warmech/lisa-cpu-card/cad/cpu-card.kicad_sch

## KiCad design cad/cpu-card.kicad_sch (2024-03-19)

Schematic: cpu-card.kicad_sch

Parts:
C1, C2, C3, C4, C5, C6, C7, C10, C11, C12, C13, C14, C15, C16, C17, C18, C20, C22, C23, C24, C25, C26, C27, C28, C29, C30, C31, C32, C33, C34, C35, C36, C37, C38, C41: 0.1uF 50V; C_Axial_L3.8mm_D2.6mm_P10.00mm_Horizontal
C8: 2.2uF; CP_Axial_L11.0mm_D5.0mm_P18.00mm_Horizontal
C9: 0.01uF; R_Axial_DIN0309_L9.0mm_D2.54mm_P12.70mm_Horizontal
C19, C21: 220pF; C_Rect_L9.0mm_W2.5mm_P7.50mm_MKT
C39: 0.1uF; R_Axial_DIN0309_L9.0mm_D2.54mm_P12.70mm_Horizontal
C40, C42: 220uF / 16V; CP_Axial_L11.0mm_D5.0mm_P18.00mm_Horizontal
C43: 0.1uF 50V; C_Rect_L9.0mm_W2.5mm_P7.50mm_MKT
CR1: 1N4148; D_DO-35_SOD27_P7.62mm_Horizontal
J1: Apple Lisa CPU Card Edge Connector; Apple_Lisa_CPU_CardEdge
J2: Conn_01x03; PinHeader_1x03_P2.54mm_Vertical
J3, J4: PinHeader_1x02_P2.54mm_Vertical
L1: L; R_Axial_DIN0309_L9.0mm_D2.54mm_P12.70mm_Horizontal
OSC1: 20.37504 MHz; Oscillator_DIP-14
Q1, Q2: PN4258; TO-92
R1, R11, R17: 1.5K; R_Axial_DIN0309_L9.0mm_D2.54mm_P12.70mm_Horizontal
R2: 470K; R_Axial_DIN0309_L9.0mm_D2.54mm_P12.70mm_Horizontal
R3: 5.1K; R_Axial_DIN0309_L9.0mm_D2.54mm_P12.70mm_Horizontal
R4, R7, R8, R13: 150; R_Axial_DIN0309_L9.0mm_D2.54mm_P12.70mm_Horizontal
R5, R6, R12: 3.3K; R_Axial_DIN0309_L9.0mm_D2.54mm_P12.70mm_Horizontal
R9, R16: 1K; R_Axial_DIN0309_L9.0mm_D2.54mm_P12.70mm_Horizontal
R10: 22; R_Axial_DIN0309_L9.0mm_D2.54mm_P12.70mm_Horizontal
R14: 330; R_Axial_DIN0309_L9.0mm_D2.54mm_P12.70mm_Horizontal
R15: 47; R_Axial_DIN0309_L9.0mm_D2.54mm_P12.70mm_Horizontal
RP1, RP2: R_Pack15_Split; DIP-16_W7.62mm
U1A1, U2D1: 74LS32; DIP-14_W7.62mm
U1B1: 74LS04; DIP-14_W7.62mm
U1C1: 74LS169; DIP-16_W7.62mm
U1D1, U13F1: 74LS138; DIP-16_W7.62mm
U1E1: 74S132; DIP-14_W7.62mm
U2B1, U3B1, U3C1, U4B1: 74LS109; DIP-16_W7.62mm
U2C1, U3D1: 74LS260; DIP-14_W7.62mm
U2E1: 7417; DIP-14_W7.62mm
U3A1, U3E1, U5D1: 74S109; DIP-16_W7.62mm
U4A1: 74LS08; DIP-14_W7.62mm
U4D1: 74S86; DIP-14_W7.62mm
U4E1: 74LS259; DIP-16_W7.62mm
U4F1: 74LS156; DIP-16_W7.62mm
U5A1: 74F10; DIP-14_W7.62mm
U5B1, U6A1: 74F02; DIP-14_W7.62mm
U5C1: 74LS279; DIP-16_W7.62mm
U5E1, U6F1, U7B1: 74LS393; DIP-14_W7.62mm
U5F1, U6E1, U7E1, U8E1: 74LS153; DIP-16_W7.62mm
U6B1, U7D1, U11C1, U11D1, U11E1, U13E1: 74LS374; DIP-20_W7.62mm
U6C1: 6309; DIP-20_W7.62mm
U6D1, U7C1, U15F1: 74LS00; DIP-14_W7.62mm
U7A1: 74LS38; DIP-14_W7.62mm
U7F1, U8F1: 74LS166; DIP-16_W7.62mm
U8A1, U9A1, U10A1: 2148H; DIP-18_W7.62mm
U8B1, U9B1, U10B1: 74F283; DIP-16_W7.62mm
U8C1, U9E1, U15C1: 74LS244; DIP-20_W7.62mm
U9D1: 74LS373; DIP-20_W7.62mm
U9F1, U11A1, U11B1, U11F1, U14E1, U15E1: 74LS245; DIP-20_W7.62mm
U10C1: 74LS11; DIP-14_W7.62mm
U12F1: 74LS148; DIP-16_W7.62mm
U13A1: 68000; DIP-64_W22.86mm
U14F1: 74LS139; DIP-16_W7.62mm
U15B1: LM556; DIP-14_W7.62mm
UD13, UD14: 2764; DIP-28_W15.24mm
Y1: Crystal; Crystal_HC18-U_Horizontal_1EP_style1

Connections:
+5V: C1.2, C2.2, C3.2, C4.2, C5.2, C6.2, C7.2, C9.1, C10.2, C11.2, C12.2, C13.2, C14.2, C15.2, C16.2, C17.2, C18.2, C20.2, C22.2, C23.2, C24.2, C25.2, C26.2, C27.2, C28.2, C29.2, C30.2, C31.2, C32.2, C33.2, C34.2, C35.2, C36.2, C37.2, C38.2, C40.1, C41.2, C42.1, CR1.1 (K), J1.19 (+5V), J1.20 (+5V), J1.45 (+5V), J1.46 (+5V), J1.91 (+5V), J1.92 (+5V), J1.119 (+5V), J1.120 (+5V), J2.3, OSC1.14 (Vcc), R1.1, R2.1, R3.1, R5.1, R6.1, R11.1, R12.1, RP1.16, RP2.16, U1A1.14 (VCC), U1B1.14 (VCC), U1C1.16 (VCC), U1D1.16 (VCC), U1E1.14 (VCC), U2B1.16 (VCC), U2C1.14 (VCC), U2D1.14 (VCC), U2E1.14 (VCC), U3A1.16 (VCC), U3B1.16 (VCC), U3C1.16 (VCC), U3D1.14 (VCC), U3E1.16 (VCC), U4A1.14 (VCC), U4B1.16 (VCC), U4D1.14 (VCC), U4E1.16 (VCC), U4F1.16 (VCC), U5A1.14 (VCC), U5B1.14 (VCC), U5C1.16 (VCC), U5D1.16 (VCC), U5E1.14 (VCC), U5F1.16 (VCC), U6A1.14 (VCC), U6B1.20 (VCC), U6C1.20 (VCC), U6D1.14 (VCC), U6E1.16 (VCC), U6F1.14 (VCC), U7A1.14 (VCC), U7B1.14 (VCC), U7C1.14 (VCC), U7D1.20 (VCC), U7E1.16 (VCC), U7F1.16 (VCC), U8A1.18 (VCC), U8B1.16 (VCC), U8C1.20 (VCC), U8E1.16 (VCC), U8F1.16 (VCC), U9A1.18 (VCC), U9B1.16 (VCC), U9D1.20 (VCC), U9E1.20 (VCC), U9F1.20 (VCC), U10A1.18 (VCC), U10B1.16 (VCC), U10C1.14 (VCC), U11A1.20 (VCC), U11B1.20 (VCC), U11C1.20 (VCC), U11D1.20 (VCC), U11E1.20 (VCC), U11F1.20 (VCC), U12F1.16 (VCC), U13A1.14 (VCC), U13A1.49 (VCC), U13E1.20 (VCC), U13F1.16 (VCC), U14E1.20 (VCC), U14F1.16 (VCC), U15B1.4 (RST), U15B1.10 (RST), U15B1.14 (VCC), U15C1.20 (VCC), U15E1.20 (VCC), U15F1.14 (VCC), UD13.1 (VPP), UD13.26 (NC), UD13.27 (~PGM), UD13.28 (VCC), UD14.26 (NC), UD14.27 (~PGM), UD14.28 (VCC)
+12V: J1.61 (+12V), R14.2, R17.2
A1: J1.47 (A1), U4E1.13 (D), U4F1.13 (A0), U7E1.6 (I0a), U15C1.3 (O3b)
A2: J1.48 (A2), U4E1.1 (A0), U4F1.3 (A1), U7E1.10 (I0b), U15C1.5 (O2b)
A3: J1.49 (A3), U4E1.2 (A1), U4F1.1 (Ea1), U4F1.15 (Eb2), U6E1.6 (I0a), U15C1.7 (O1b)
A4: J1.50 (A4), U4E1.3 (A2), U6E1.10 (I0b), U15C1.9 (O0b)
A5: J1.51 (A5), U5F1.6 (I0a), U15C1.12 (O3a)
A6: J1.52 (A6), U5F1.10 (I0b), U11E1.4 (D1), U15C1.14 (O2a)
A7: J1.53 (A7), U8E1.6 (I0a), U11E1.7 (D2), U15C1.16 (O1a)
A8: J1.54 (A8), U8E1.10 (I0b), U11E1.8 (D3), U15C1.18 (O0a)
A9: J1.55 (A9), U7E1.4 (I2a), U11D1.12 (O4), U11E1.13 (D4)
A10: J1.56 (A10), U7E1.12 (I2b), U11D1.15 (O5), U11E1.14 (D5)
A11: J1.57 (A11), U6E1.4 (I2a), U11D1.16 (O6), U11E1.17 (D6), U14F1.14 (A0)
A12: J1.58 (A12), U6E1.12 (I2b), U11D1.19 (O7), U11E1.18 (D7), U14F1.13 (A1)
A13: U5F1.4 (I2a), U7D1.2 (O0), U9D1.2 (O0), U13E1.3 (D0)
A14: U5F1.12 (I2b), U7D1.5 (O1), U9D1.5 (O1), U13E1.4 (D1)
A15: U7D1.6 (O2), U8E1.3 (I3a), U8E1.4 (I2a), U9D1.6 (O2), U11C1.6 (O2), U13E1.7 (D2)
A16: J1.102 (A16), U7D1.9 (O3), U8E1.12 (I2b), U8E1.13 (I3b), U9D1.9 (O3), U11C1.9 (O3), U13E1.8 (D3)
A17: J1.103 (A17), U7D1.12 (O4), U9D1.12 (O4), U11C1.12 (O4), U13E1.13 (D4)
A18: J1.104 (A18), U7D1.15 (O5), U9D1.15 (O5), U11C1.15 (O5), U13E1.14 (D5)
A19: J1.105 (A19), U7D1.16 (O6), U9D1.16 (O6), U11C1.16 (O6), U13E1.17 (D6)
A20: J1.110 (A20), U7D1.19 (O7), U9D1.19 (O7), U11C1.19 (O7), U13E1.18 (D7)
ACCK: U3D1.3, U4D1.1, U9B1.9 (C4), U10B1.7 (C0)
AS: U2B1.15 (~R), U2E1.13, U3A1.5 (~S), U3B1.1 (~R), U3B1.15 (~R), U4B1.1 (~R), U6A1.1
BD0: J1.27 (BD0), U9E1.18 (O0a), U9F1.18 (B0), U11E1.2 (O0), U15E1.2 (A0)
BD1: J1.28 (BD1), U9E1.16 (O1a), U9F1.17 (B1), U11E1.5 (O1), U15E1.3 (A1)
BD2: J1.29 (BD2), U9E1.14 (O2a), U9F1.16 (B2), U11E1.6 (O2), U15E1.4 (A2)
BD3: J1.30 (BD3), U9E1.12 (O3a), U9F1.15 (B3), U11E1.9 (O3), U15E1.5 (A3)
BD4: J1.31 (BD4), U9E1.9 (O0b), U9F1.14 (B4), U11E1.12 (O4), U15E1.6 (A4)
BD5: J1.32 (BD5), U7D1.3 (D0), U9E1.7 (O1b), U9F1.13 (B5), U11E1.15 (O5), U15E1.7 (A5)
BD6: J1.33 (BD6), U7D1.4 (D1), U9E1.5 (O2b), U9F1.12 (B6), U11E1.16 (O6), U15E1.8 (A6)
BD7: J1.34 (BD7), U7D1.7 (D2), U9E1.3 (O3b), U9F1.11 (B7), U11E1.19 (O7), U15E1.9 (A7)
BD8: J1.35 (BD8), U7D1.8 (D3), U11F1.18 (B0), U13E1.2 (O0), U14E1.2 (A0)
BD9: J1.36 (BD9), U7D1.13 (D4), U11F1.17 (B1), U13E1.5 (O1), U14E1.3 (A1)
BD10: J1.37 (BD10), U7D1.14 (D5), U11F1.16 (B2), U13E1.6 (O2), U14E1.4 (A2)
BD11: J1.38 (BD11), U7D1.17 (D6), U11F1.15 (B3), U13E1.9 (O3), U14E1.5 (A3)
BD12: J1.39 (BD12), U7D1.18 (D7), U11F1.14 (B4), U13E1.12 (O4), U14E1.6 (A4)
BD13: J1.40 (BD13), U11F1.13 (B5), U13E1.15 (O5), U14E1.7 (A5)
BD14: J1.41 (BD14), U11F1.12 (B6), U13E1.16 (O6), U14E1.8 (A6)
BD15: J1.42 (BD15), U11F1.11 (B7), U13E1.19 (O7), U14E1.9 (A7)
BGACK: U3D1.1, U3D1.8, U6A1.13, U6D1.4, U7C1.12, U8C1.19 (OEb), U11D1.1 (OE), U15C1.1 (OEa), U15C1.19 (OEb)
CAS: U2C1.1, U3A1.4 (C), U3C1.9 (~Q), U10C1.3
CK: U1C1.2 (CP), U1E1.6, U2B1.4 (C), U2B1.12 (C), U3A1.12 (C), U3B1.4 (C), U3B1.12 (C), U3C1.4 (C), U3C1.12 (C), U4B1.4 (C), U4B1.12 (C)
CMUX: U2D1.10, U4A1.4, U4B1.10 (Q), U6D1.5, U11C1.1 (OE), U15F1.10
CPUC1: U1A1.1, U2B1.6 (Q), U5A1.9, U7C1.13
CPUCK: J1.22 (CPUCK), R10.1
DOTCK: J1.106 (DOTCK), U1E1.8, U3E1.4 (C), U3E1.12 (C), U5D1.4 (C), U5D1.12 (C), U7F1.7 (Clk), U8F1.7 (Clk)
E: J1.16 (E), U8C1.14 (O2a)
FC2: U7C1.2, U10C1.11, U13A1.26 (FC2)
GND: C1.1, C2.1, C3.1, C4.1, C5.1, C6.1, C7.1, C8.2, C10.1, C11.1, C12.1, C13.1, C14.1, C15.1, C16.1, C17.1, C18.1, C19.2, C20.1, C21.2, C22.1, C23.1, C24.1, C25.1, C26.1, C27.1, C28.1, C29.1, C30.1, C31.1, C32.1, C33.1, C34.1, C35.1, C36.1, C37.1, C38.1, C39.2, C40.2, C41.1, C42.2, C43.2, J1.17 (GND), J1.18 (GND), J1.43 (GND), J1.44 (GND), J1.89 (GND), J1.90 (GND), J1.117 (GND), J1.118 (GND), J3.1, J4.1, L1.2, OSC1.7 (GND), R9.1, R13.2, R16.2, U1A1.7 (GND), U1B1.7 (GND), U1C1.3 (P0), U1C1.4 (P1), U1C1.5 (P2), U1C1.6 (P3), U1C1.7 (~CEP), U1C1.8 (GND), U1C1.10 (~CET), U1D1.4 (E1), U1D1.5 (E2), U1D1.8 (GND), U1E1.7 (GND), U2B1.8 (GND), U2C1.7 (GND), U2D1.7 (GND), U2E1.7 (GND), U3A1.2 (J), U3A1.8 (GND), U3B1.8 (GND), U3C1.8 (GND), U3D1.7 (GND), U3E1.8 (GND), U4A1.7 (GND), U4A1.9, U4A1.10, U4B1.8 (GND), U4D1.7 (GND), U4D1.12, U4E1.8 (GND), U4F1.8 (GND), U5A1.7 (GND), U5B1.7 (GND), U5C1.8 (GND), U5D1.2 (J), U5D1.8 (GND), U5E1.7 (GND), U5F1.1 (Ea), U5F1.8 (GND), U5F1.15 (Eb), U6A1.7 (GND), U6B1.1 (OE), U6B1.10 (GND), U6C1.10 (GND), U6C1.15 (/E1(P)), U6C1.16 (/E2), U6D1.7 (GND), U6E1.1 (Ea), U6E1.8 (GND), U6E1.15 (Eb), U6F1.7 (GND), U7A1.7 (GND), U7B1.7 (GND), U7C1.7 (GND), U7D1.10 (GND), U7E1.1 (Ea), U7E1.8 (GND), U7E1.15 (Eb), U7F1.8 (GND), U8A1.8 (/CS), U8A1.9 (GND), U8B1.8 (GND), U8C1.1 (OEa), U8C1.10 (GND), U8E1.1 (Ea), U8E1.8 (GND), U8E1.15 (Eb), U8F1.8 (GND), U9A1.8 (/CS), U9A1.9 (GND), U9B1.8 (GND), U9D1.10 (GND), U9E1.10 (GND), U9F1.10 (GND), U10A1.9 (GND), U10B1.2 (B2), U10B1.6 (B1), U10B1.8 (GND), U10B1.11 (B4), U10B1.15 (B3), U10C1.7 (GND), U11A1.10 (GND), U11B1.10 (GND), U11C1.3 (D0), U11C1.4 (D1), U11C1.10 (GND), U11D1.10 (GND), U11E1.10 (GND), U11F1.10 (GND), U12F1.5 (EI), U12F1.8 (GND), U13A1.16 (GND), U13A1.53 (GND), U13E1.10 (GND), U13F1.8 (GND), U14E1.10 (GND), U14F1.8 (GND), U15B1.7 (GND), U15C1.10 (GND), U15E1.10 (GND), U15F1.7 (GND), UD13.14 (GND), UD13.20 (~CE), UD14.14 (GND), UD14.20 (~CE)
IAK: U1B1.5, U2C1.9, U10C1.8
INVID: J3.2, RP1.10, U4D1.10, U8F1.1 (Ds), U9E1.15 (I2b)
IOA13: U11D1.2 (O0), U13F1.1 (A0)
IOA14: U11D1.5 (O1), U13F1.2 (A1)
IOA15: U11D1.6 (O2), U13F1.3 (A2)
IOA16: RP2.5, U11D1.9 (O3), U13F1.5 (E2)
IOCY: U2C1.2, U2C1.8, U3A1.13 (~K), U3A1.14 (J), U3A1.15 (~R), U4B1.6 (Q)
MALE: U2B1.9 (~Q), U9D1.11 (LE)
MD0: J1.73 (MD0), U8F1.2 (A), U9F1.2 (A0)
MD1: J1.74 (MD1), U8F1.3 (B), U9F1.3 (A1)
MD2: J1.75 (MD2), U8F1.4 (C), U9F1.4 (A2)
MD3: J1.76 (MD3), U8F1.5 (D), U9F1.5 (A3)
MD4: J1.77 (MD4), U8F1.10 (E), U9F1.6 (A4)
MD5: J1.78 (MD5), U8F1.11 (F), U9F1.7 (A5)
MD6: J1.79 (MD6), U8F1.12 (G), U9F1.8 (A6)
MD7: J1.80 (MD7), U8F1.14 (H), U9F1.9 (A7)
MD8: J1.81 (MD8), U7F1.2 (A), U11F1.2 (A0)
MD9: J1.82 (MD9), U7F1.3 (B), U11F1.3 (A1)
MD10: J1.83 (MD10), U7F1.4 (C), U11F1.4 (A2)
MD11: J1.84 (MD11), U7F1.5 (D), U11F1.5 (A3)
MD12: J1.85 (MD12), U7F1.10 (E), U11F1.6 (A4)
MD13: J1.86 (MD13), U7F1.11 (F), U11F1.7 (A5)
MD14: J1.87 (MD14), U7F1.12 (G), U11F1.8 (A6)
MD15: J1.88 (MD15), U7F1.14 (H), U11F1.9 (A7)
MMUIO: U1A1.4, U1B1.12, U5D1.5 (~S), U5D1.11 (~S), U6D1.12
MREAD: J1.107 (MREAD), U1E1.11
unnamed: C9.2, R3.2, U2E1.12, U15B1.8 (TRG), U15B1.12 (THR)
unnamed: C19.1, R4.2, R5.2, U5C1.1 (/1R)
unnamed: C21.1, R6.2, R7.2, U5C1.10 (/3R)
unnamed: C39.1, Q1.2 (B), R15.2, R16.1, R17.1
unnamed: L1.1, Q1.3 (C), Y1.1
unnamed: OSC1.8 (OUT), Q2.3 (C), R13.1, U1E1.2
unnamed: Q1.1 (E), Q2.1 (E), R14.1
unnamed: Q2.2 (B), R15.1, Y1.2
unnamed: R8.1, U11A1.9 (A7)
unnamed: R9.2, U10C1.10, U13A1.28 (FC0)
unnamed: R10.2, U4D1.11
unnamed: RP1.2, U1C1.9 (~PE)
unnamed: RP1.3, U9E1.17 (I3b)
unnamed: RP1.6, U1E1.1
unnamed: RP1.8, U1E1.5, U1E1.9
unnamed: RP1.11, U1C1.1 (U/~D), U1D1.6 (E3)
unnamed: RP2.4, U3E1.1 (~R), U3E1.11 (~S), U3E1.15 (~R), U7F1.9 (Clr), U8F1.9 (Clr)
unnamed: RP2.11, U2E1.2, U2E1.3, U13A1.18 (RESET)
unnamed: U1A1.3, U3C1.5 (~S)
unnamed: U1A1.6, U5B1.11
unnamed: U1A1.9, U1A1.10, U1A1.11
unnamed: U1A1.8, U1A1.12, U1A1.13
unnamed: U1B1.2, U3C1.2 (J)
unnamed: U1B1.4, U3C1.14 (J)
unnamed: U1B1.6, U2D1.12
unnamed: U1B1.10, U3D1.11
unnamed: U1C1.12 (Q2), U1D1.3 (A2)
unnamed: U1C1.14 (Q0), U1D1.1 (A0)
unnamed: U1E1.3, U1E1.4, U1E1.10
unnamed: U1E1.12, U1E1.13, U5B1.4, U7A1.9, U7A1.12
unnamed: U2B1.2 (J), U2B1.14 (J), U2C1.6
unnamed: U2C1.5, U3B1.14 (J)
unnamed: U2C1.11, U3B1.10 (Q)
unnamed: U2D1.3, U5A1.2
unnamed: U2D1.6, U5D1.13 (~K)
unnamed: U2D1.11, U4F1.2 (Ea2), U4F1.14 (Eb1)
unnamed: U2E1.5, U3A1.6 (Q)
unnamed: U3A1.7 (~Q), U6A1.8
unnamed: U3B1.2 (J), U3D1.6
unnamed: U3C1.11 (~S), U5A1.6
unnamed: U3D1.4, U5A1.1, U5B1.1
unnamed: U3D1.5, U4B1.2 (J)
unnamed: U3E1.5 (~S), U4A1.11
unnamed: U3E1.6 (Q), U6F1.1 (CP), U7F1.15 (PE), U8F1.15 (PE)
unnamed: U3E1.10 (Q), U4D1.9
unnamed: U3E1.13 (~K), U3E1.14 (J), U7F1.13 (Qh)
unnamed: U4A1.2, U6C1.9 (O4)
unnamed: U4A1.3, U6B1.8 (D3)
unnamed: U4A1.5, U6B1.9 (O3)
unnamed: U4A1.6, U5E1.2 (MR), U5E1.12 (MR), U6F1.2 (MR), U6F1.12 (MR)
unnamed: U4A1.13, U6B1.6 (O2)
unnamed: U4B1.14 (J), U6A1.4
unnamed: U4D1.3, U5A1.13
unnamed: U4E1.4 (Q0), U7A1.10
unnamed: U4E1.5 (Q1), U7A1.13
unnamed: U5A1.4, U7C1.11
unnamed: U5A1.5, U5A1.12
unnamed: U5B1.10, U8B1.7 (C0)
unnamed: U5C1.13 (4Q), U9E1.8 (I3a)
unnamed: U5E1.9 (Q2), U6C1.19 (A7), U6D1.2, U7F1.6 (CE), U8F1.6 (CE)
unnamed: U6B1.2 (O0), U7B1.2 (MR), U7B1.12 (MR)
unnamed: U6B1.3 (D0), U6C1.6 (O1)
unnamed: U6B1.4 (D1), U6C1.7 (O2)
unnamed: U6B1.7 (D2), U6C1.8 (O3)
unnamed: U6B1.13 (D4), U6C1.11 (O5)
unnamed: U6B1.14 (D5), U6C1.12 (O6)
unnamed: U6B1.15 (O5), U6D1.1
unnamed: U6B1.17 (D6), U6B1.18 (D7), U6C1.13 (O7)
unnamed: U6C1.1 (A0), U7B1.3 (Q0)
unnamed: U6C1.2 (A1), U7B1.4 (Q1)
unnamed: U6C1.3 (A2), U7B1.5 (Q2)
unnamed: U6C1.4 (A3), U7B1.6 (Q3), U7B1.13 (CP)
unnamed: U6C1.5 (A4), U7B1.11 (Q0)
unnamed: U6C1.17 (A5), U7B1.10 (Q1)
unnamed: U6D1.6, U7D1.1 (OE)
unnamed: U6D1.10, U6D1.11
unnamed: U7C1.3, U7C1.4, U7C1.10
unnamed: U7F1.1 (Ds), U8F1.13 (Qh)
unnamed: U8B1.9 (C4), U9B1.7 (C0)
unnamed: U7C1.8, U8A1.4 (A3), U9A1.4 (A3), U10A1.4 (A3)
unnamed: U7C1.6, U8A1.5 (A0), U9A1.5 (A0), U10A1.5 (A0)
unnamed: U5B1.8, U6D1.8, U8A1.6 (A1), U9A1.6 (A1), U10A1.6 (A1)
unnamed: U5B1.13, U10A1.8 (/CS)
unnamed: U5D1.10 (Q), U8A1.10 (/WE), U9A1.10 (/WE), U10A1.10 (/WE)
unnamed: U9D1.14 (D5), U10B1.1 (S2)
unnamed: U9D1.13 (D4), U10B1.4 (S1)
unnamed: U9D1.18 (D7), U10B1.10 (S4)
unnamed: U9D1.17 (D6), U10B1.13 (S3)
unnamed: U5C1.9 (3Q), U9E1.4 (I1a), U10C1.1, U10C1.4
unnamed: U5C1.4 (1Q), U9E1.2 (I0a), U10C1.2, U10C1.5
unnamed: U10C1.6, U11E1.11 (Cp), U13E1.11 (Cp)
unnamed: U10C1.9, U13A1.27 (FC1)
unnamed: U5D1.6 (Q), U11A1.19 (CE), U11B1.19 (CE)
unnamed: U11C1.11 (Cp), U15F1.11
unnamed: U9B1.4 (S1), U9D1.3 (D0), U11D1.3 (D0)
unnamed: U9B1.1 (S2), U9D1.4 (D1), U11D1.4 (D1)
unnamed: U9B1.13 (S3), U9D1.7 (D2), U11D1.7 (D2)
unnamed: U9B1.10 (S4), U9D1.8 (D3), U11D1.8 (D3)
unnamed: U8B1.4 (S1), U11D1.13 (D4)
unnamed: U8B1.1 (S2), U11D1.14 (D5)
unnamed: U8B1.13 (S3), U11D1.17 (D6)
unnamed: U8B1.10 (S4), U11D1.18 (D7)
unnamed: U12F1.6 (S2), U13A1.23 (IPL2)
unnamed: U12F1.7 (S1), U13A1.24 (IPL1)
unnamed: U12F1.9 (S0), U13A1.25 (IPL0)
unnamed: U8C1.17 (I3b), U13A1.7 (UDS)
unnamed: U8C1.15 (I2b), U13A1.8 (LDS)
unnamed: U8C1.11 (I0b), U13A1.9 (R/W)
unnamed: U8C1.8 (I3a), U13A1.19 (VMA)
unnamed: U8C1.6 (I2a), U13A1.20 (E)
unnamed: U3A1.10 (Q), U13F1.6 (E3)
unnamed: U2E1.9, U13F1.7 (O7), U14F1.15 (E)
unnamed: U4E1.14 (E), U14F1.12 (O0)
unnamed: U2D1.9, U4D1.6, U15F1.2
unnamed: U9D1.1 (OE), U15F1.8
PCK: U1C1.13 (Q1), U1D1.2 (A1), U4D1.13, U5D1.14 (J), U13A1.15 (CLK)
POR: U7A1.1, U7A1.2, U15B1.5 (Q)
R1: J1.71 (R1), U15F1.3
R2: J1.72 (R2), U2D1.8
RA1: J1.93 (RA1), U7E1.7 (Za)
RA2: J1.94 (RA2), U7E1.9 (Zb)
RA3: J1.95 (RA3), U6E1.7 (Za)
RA4: J1.96 (RA4), U6E1.9 (Zb)
RA5: J1.97 (RA5), U5F1.7 (Za)
RA6: J1.98 (RA6), U5F1.9 (Zb)
RA7: J1.99 (RA7), U8E1.7 (Za)
RA8: J1.100 (RA8), U8E1.9 (Zb)
RAS: U3C1.7 (~Q), U5F1.2 (S1), U6E1.2 (S1), U7E1.2 (S1), U8E1.2 (S1)
READ: J1.64 (READ), RP2.15, U2D1.1, U2D1.5, U5B1.6, U8C1.9 (O0b), U9F1.1 (A->B), U11A1.1 (A->B), U11B1.1 (A->B), U11F1.1 (A->B), U14E1.1 (A->B), U15E1.1 (A->B)
RP1_5: RP1.5, U2B1.1 (~R), U2B1.5 (~S), U2B1.11 (~S), U2B1.13 (~K), U3A1.11 (~S), U3B1.3 (~K), U3B1.5 (~S), U3B1.13 (~K), U3C1.1 (~R), U3C1.15 (~R), U4B1.3 (~K), U4B1.5 (~S), U4B1.11 (~S), U4B1.15 (~R), U5D1.1 (~R), U5D1.15 (~R)
SEG1: U4E1.6 (Q2), U7C1.5
SEG2: U4E1.7 (Q3), U7C1.9
SN: R8.2, U6C1.14 (O8)
SPIO: U2C1.13, U3B1.6 (Q), U6A1.9
TD0: U8A1.14 (I/O1), U8B1.5 (A1), U11B1.2 (A0)
TD1: U8A1.13 (I/O2), U8B1.3 (A2), U11B1.3 (A1)
TD2: U8A1.12 (I/O3), U8B1.14 (A3), U11B1.4 (A2)
TD3: U8A1.11 (I/O4), U8B1.12 (A4), U11B1.5 (A3)
TD4: U9A1.14 (I/O1), U9B1.5 (A1), U11B1.6 (A4)
TD5: U9A1.13 (I/O2), U9B1.3 (A2), U11B1.7 (A5)
TD6: U9A1.12 (I/O3), U9B1.14 (A3), U11B1.8 (A6)
TD7: U9A1.11 (I/O4), U9B1.12 (A4), U11B1.9 (A7)
UA1: U13A1.29 (A1), U15C1.17 (I3b), UD13.10 (A0), UD14.10 (A0)
UA2: U13A1.30 (A2), U15C1.15 (I2b), UD13.9 (A1), UD14.9 (A1)
UA3: U6D1.13, U13A1.31 (A3), U15C1.13 (I1b), UD13.8 (A2), UD14.8 (A2)
UA4: U13A1.32 (A4), U15C1.11 (I0b), UD13.7 (A3), UD14.7 (A3)
UA5: U13A1.33 (A5), U15C1.8 (I3a), UD13.6 (A4), UD14.6 (A4)
UA6: U13A1.34 (A6), U15C1.6 (I2a), UD13.5 (A5), UD14.5 (A5)
UA7: U13A1.35 (A7), U15C1.4 (I1a), UD13.4 (A6), UD14.4 (A6)
UA8: U13A1.36 (A8), U15C1.2 (I0a), UD13.3 (A7), UD14.3 (A7)
UA9: U8B1.6 (B1), U13A1.37 (A9), UD13.25 (A8), UD14.25 (A8)
UA10: U8B1.2 (B2), U13A1.38 (A10), UD13.24 (A9), UD14.24 (A9)
UA11: U8B1.15 (B3), U13A1.39 (A11), UD13.21 (A10), UD14.21 (A10)
UA12: J2.1, J2.2, U8B1.11 (B4), U13A1.40 (A12), UD13.23 (A11), UD14.23 (A11)
UA13: U9B1.6 (B1), U13A1.41 (A13), UD13.2 (A12), UD14.2 (A12)
UA14: U5B1.12, U9B1.2 (B2), U13A1.42 (A14)
UA15: U9B1.15 (B3), U13A1.43 (A15), U14F1.2 (A0)
UA16: U9B1.11 (B4), U13A1.44 (A16), U14F1.3 (A1)
UA17: U8A1.17 (A7), U9A1.17 (A7), U10A1.17 (A7), U13A1.45 (A17)
UA18: U8A1.16 (A8), U9A1.16 (A8), U10A1.16 (A8), U13A1.46 (A18)
UA19: U8A1.15 (A9), U9A1.15 (A9), U10A1.15 (A9), U13A1.47 (A19)
UA20: U8A1.7 (A2), U9A1.7 (A2), U10A1.7 (A2), U13A1.48 (A20)
UA21: U8A1.1 (A6), U9A1.1 (A6), U10A1.1 (A6), U13A1.50 (A21)
UA22: U8A1.2 (A5), U9A1.2 (A5), U10A1.2 (A5), U13A1.51 (A22)
UA23: U8A1.3 (A4), U9A1.3 (A4), U10A1.3 (A4), U13A1.52 (A23)
UD0: U11B1.18 (B0), U11C1.7 (D2), U13A1.5 (D0), U15E1.18 (B0), UD14.11 (D0)
UD1: U11B1.17 (B1), U11C1.8 (D3), U13A1.4 (D1), U15E1.17 (B1), UD14.12 (D1)
UD2: U11B1.16 (B2), U11C1.13 (D4), U13A1.3 (D2), U15E1.16 (B2), UD14.13 (D2)
UD3: U11B1.15 (B3), U11C1.14 (D5), U13A1.2 (D3), U15E1.15 (B3), UD14.15 (D3)
UD4: U11B1.14 (B4), U11C1.17 (D6), U13A1.1 (D4), U15E1.14 (B4), UD14.16 (D4)
UD5: U11B1.13 (B5), U11C1.18 (D7), U13A1.64 (D5), U15E1.13 (B5), UD14.17 (D5)
UD6: U11B1.12 (B6), U13A1.63 (D6), U15E1.12 (B6), UD14.18 (D6)
UD7: U11B1.11 (B7), U13A1.62 (D7), U15E1.11 (B7), UD14.19 (D7)
UD8: U11A1.18 (B0), U13A1.61 (D8), U14E1.18 (B0), UD13.11 (D0)
UD9: U11A1.17 (B1), U13A1.60 (D9), U14E1.17 (B1), UD13.12 (D1)
UD10: U11A1.16 (B2), U13A1.59 (D10), U14E1.16 (B2), UD13.13 (D2)
UD11: U11A1.15 (B3), U13A1.58 (D11), U14E1.15 (B3), UD13.15 (D3)
UD12: U13A1.57 (D12), U14E1.14 (B4), UD13.16 (D4)
UD13: U13A1.56 (D13), U14E1.13 (B5), UD13.17 (D5)
UD14: U11A1.12 (B6), U13A1.55 (D14), U14E1.12 (B6), UD13.18 (D6)
UD15: U11A1.11 (B7), U13A1.54 (D15), U14E1.11 (B7), UD13.19 (D7)
VA1: U6F1.3 (Q0), U7E1.5 (I1a)
VA2: U6F1.4 (Q1), U7E1.11 (I1b)
VA3: U6E1.5 (I1a), U6F1.5 (Q2)
VA4: U6E1.11 (I1b), U6F1.6 (Q3), U6F1.13 (CP)
VA5: U5F1.5 (I1a), U6F1.11 (Q0)
VA6: U5F1.11 (I1b), U6F1.10 (Q1)
VA7: U6F1.9 (Q2), U8E1.5 (I1a)
VA8: U4A1.1, U4D1.4, U5E1.1 (CP), U6F1.8 (Q3), U8E1.11 (I1b)
VA9: U5E1.3 (Q0), U6C1.18 (A6), U7E1.3 (I3a), U8C1.2 (I0a)
VA9B: J1.70 (VA9B), U8C1.18 (O0a)
VA10: U5E1.4 (Q1), U7E1.13 (I3b), U8C1.4 (I1a)
VA10B: J1.69 (VA10B), U8C1.16 (O1a)
VA11: U4D1.5, U5E1.5 (Q2), U6E1.3 (I3a)
VA12: U5E1.6 (Q3), U5E1.13 (CP), U6E1.13 (I3b)
VA13: U5E1.11 (Q0), U5F1.3 (I3a)
VA14: U5E1.10 (Q1), U5F1.13 (I3b)
VID: J1.115 (VID), U4D1.8, U9E1.11 (I0b)
VIDEO: U1A1.2, U1B1.9, U1C1.11 (Q3), U3A1.3 (~K), U4A1.12, U6B1.11 (Cp), U7B1.1 (CP), U11E1.3 (D0)
/AS: J1.63 (/AS), RP1.7, U2C1.4, U6A1.2, U6A1.3, U8C1.7 (O1b)
/BERR: U3B1.9 (~Q), U13A1.22 (BERR)
/BG: J1.26 (/BG), U13A1.11 (BG)
/BGACK: J1.24 (/BGACK), RP1.4, U6A1.11, U6A1.12, U13A1.12 (BGACK), U15F1.5, U15F1.9
/BR: J1.25 (/BR), RP2.12, U13A1.13 (BR)
/BUST: U3B1.11 (~S), U5C1.14 (/4R), U15B1.9 (DIS)
/CAS: J1.108 (/CAS), U3C1.10 (Q)
/CDACK: U6A1.10, U13A1.10 (DTACK)
/CMUX: U4B1.9 (~Q), U5F1.14 (S0), U6E1.14 (S0), U7E1.14 (S0), U8E1.14 (S0), U15F1.1
/CPUC1: U2B1.7 (~Q), U2C1.3, U3D1.9, U3D1.13, U5B1.3, U5B1.5
/CSYNC: J1.67 (/CSYNC), U6B1.12 (O4), U9E1.13 (I1b)
/DBON: U14E1.19 (CE), U15E1.19 (CE), U15F1.6
/DTACK: J1.62 (/DTACK), R1.2, U2E1.6, U2E1.8, U3A1.1 (~R)
/HALT: RP1.12, U2E1.1, U4E1.15 (Clr), U7A1.3, U13A1.17 (HALT)
/HDER: J1.112 (/HDER), R7.1, U7A1.11
/HDMSK: C43.1, U4E1.12 (Q7), U5C1.11 (/3S1), U5C1.12 (/3S2)
/HPIR: U10C1.12, U12F1.4 (I7)
/HSYNC: J1.111 (/HSYNC), U6B1.16 (O6)
/IAK0: J1.8 (/IAK0), U4F1.6 (Q1a)
/IAK1: J1.10 (/IAK1), U4F1.7 (Q0a)
/IAK2: J1.12 (/IAK2), U4F1.12 (Q3b)
/INT0: J1.7 (/INT0), RP2.7, U12F1.2 (I5)
/INT1: J1.9 (/INT1), RP2.8, U12F1.1 (I4)
/INT2: J1.11 (/INT2), RP2.9, U12F1.13 (I3)
/INTIO: J1.68 (/INITIO), U13F1.9 (O6)
/IO: RP1.1, U3D1.2, U10A1.12 (I/O3), U10B1.14 (A3), U11A1.4 (A2)
/IOCY: U4B1.7 (~Q), U5A1.10
/IOIR: J1.15 (/IOIR), RP2.10, U2E1.10, U12F1.10 (IO), U12F1.11 (I1)
/KBIR: J1.14 (/KBIR), RP2.14, U12F1.12 (I2)
/LDMA: J1.23 (/LDMA), R11.2, U7D1.11 (Cp)
/LDS: J1.65 (/LDS), RP2.1, U8C1.5 (O2b)
/MALE: U2B1.10 (Q), U6D1.9, U11D1.11 (Cp)
/MDEN: U5A1.8, U9F1.19 (CE), U11F1.19 (CE)
/MEM: RP1.15, U5B1.2, U10A1.11 (I/O4), U10B1.12 (A4), U11A1.5 (A3)
/MMUIO: U1B1.13, U7C1.1, U14F1.5 (O1)
/NMI: J1.116 (/NMI), RP2.6, U10C1.13
/RAS: J1.109 (/RAS), U3C1.6 (Q)
/RBES: U9E1.1 (OEa), U9E1.19 (OEb), U14F1.9 (O3)
/RESET: J1.21 (/RESET), R12.2, U2E1.4
/RMEA: U5C1.15 (/4S), U11E1.1 (OE), U13E1.1 (OE), U14F1.10 (O2)
/RO: RP1.14, U1B1.11, U2D1.2, U10A1.13 (I/O2), U10B1.3 (A2), U11A1.3 (A1)
/ROM: U14F1.4 (O0), UD13.22 (~OE), UD14.22 (~OE)
/RSIR: J1.13 (/RSIR), RP2.13, U12F1.3 (I6)
/RSTSW: C8.1, CR1.2 (A), J1.101 (/RSTSW), J4.2, R2.2, U15B1.2 (THR), U15B1.6 (TRG)
/SFER: J1.114 (/SFER), R4.1, U7A1.8
/SFMSK: U4E1.10 (Q5), U5C1.2 (/1S1), U5C1.3 (/1S2)
/SH0: J1.2 (/SH0), U13F1.14 (O1)
/SH1: J1.4 (/SH1), U13F1.12 (O3)
/SH2: J1.6 (/SH2), U13F1.10 (O5)
/SL0: J1.1 (/SL0), U13F1.15 (O0)
/SL1: J1.3 (/SL1), U13F1.13 (O2)
/SL2: J1.5 (/SL2), U13F1.11 (O4)
/SPIO: U3B1.7 (~Q), U5A1.11, U14F1.1 (E), U15F1.4
/START: U1A1.5, U4E1.9 (Q4)
/STK: RP1.9, U4D1.2, U5B1.9, U10A1.14 (I/O1), U10B1.5 (A1), U11A1.2 (A0)
/T0: U1D1.15 (O0), U3C1.3 (~K)
/T1: U1D1.14 (O1)
/T2: U1D1.13 (O2), U3C1.13 (~K), U3D1.10, U3D1.12
/T3: U1D1.12 (O3), U2C1.12
/T4: U1D1.11 (O4), U2D1.4, U5D1.3 (~K)
/T5: U1B1.1, U1D1.10 (O5)
/T6: U1B1.3, U1D1.9 (O6), U3E1.2 (J), U3E1.3 (~K), U4B1.13 (~K), U6A1.6
/T7: U1D1.7 (O7)
/UAS: RP2.3, U2D1.13, U8C1.13 (I1b), U13A1.6 (AS), U13F1.4 (E1)
/UDS: J1.66 (/UDS), RP2.2, U8C1.3 (O3b)
/VAL: U14F1.11 (O1), U15F1.12, U15F1.13
/VIDEO: U1B1.8, U2B1.3 (~K), U5A1.3, U6A1.5
/VMA: J1.59 (/VMA), U8C1.12 (O3a)
/VPA: J1.60 (/VPA), RP1.13, U4F1.4 (Q3a), U4F1.5 (Q2a), U4F1.9 (Q0b), U4F1.10 (Q1b), U4F1.11 (Q2b), U13A1.21 (VPA)
/VSIR: U5C1.5 (/2R), U6D1.3
/VSYNC: J1.113 (/VSYNC), U6B1.5 (O1)
/VT7: U1C1.15 (~TC), U2C1.10
/VTIR: U2E1.11, U5C1.7 (2Q), U9E1.6 (I2a)
/VTMSK: U4E1.11 (Q6), U5C1.6 (/2S)

Notes on the sheet:
CPU
MEMORY MANAGEMENT UNIT
VIDEO
DECOUPLING CAPACITORS
POWER CONNECTIONS
UNUSED
CONNECTOR
CLOCK & I/O
